fenrir-naru/gpib-usbcdc/firmware/f38x_usb.c

/*
 * Copyright (c) 2015, M.Naruoka (fenrir)
 * All rights reserved.
 *
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
 * THIS SOFTWARE IS PROVIDED BY THE COPYRIGHT HOLDERS AND CONTRIBUTORS "AS IS"
 * AND ANY EXPRESS OR IMPLIED WARRANTIES, INCLUDING, BUT NOT LIMITED TO,
 * THE IMPLIED WARRANTIES OF MERCHANTABILITY AND FITNESS FOR A PARTICULAR PURPOSE
 * ARE DISCLAIMED. IN NO EVENT SHALL THE COPYRIGHT HOLDER OR CONTRIBUTORS
 * BE LIABLE FOR ANY DIRECT, INDIRECT, INCIDENTAL, SPECIAL, EXEMPLARY,
 * OR CONSEQUENTIAL DAMAGES (INCLUDING, BUT NOT LIMITED TO,
 * PROCUREMENT OF SUBSTITUTE GOODS OR SERVICES;
 * LOSS OF USE, DATA, OR PROFITS; OR BUSINESS INTERRUPTION)
 * HOWEVER CAUSED AND ON ANY THEORY OF LIABILITY, WHETHER IN CONTRACT,
 * STRICT LIABILITY, OR TORT (INCLUDING NEGLIGENCE OR OTHERWISE)
 * ARISING IN ANY WAY OUT OF THE USE OF THIS SOFTWARE,
 * EVEN IF ADVISED OF THE POSSIBILITY OF SUCH DAMAGE.
 *
 */

#include <stdio.h>
#include <string.h>

#include "c8051f380.h"
#include "main.h"
#include "f38x_usb_register.h"
#include "f38x_usb.h"
#include "usb_descriptor.h"

#include "usb_std_req.h"
#include "usb_other_req.h"

#include "usb_cdc.h"

#include "util.h"

// Holds the current USB State
usb_state_t usb_state;

ep0_setup_t ep0_setup;
ep0_data_t ep0_data;
volatile __bit ep0_request_completed;

// Holds the status for each endpoint
BYTE __xdata usb_ep_stat[7];

static __xdata unsigned int ep_out_stored[3];
#define count_ep_out(index) ep_out_stored[index - 1]

static const __code unsigned int ep_size[] = {
  PACKET_SIZE_EP0,
  PACKET_SIZE_EP1,
  PACKET_SIZE_EP2,
  PACKET_SIZE_EP3
};

static __code void(* __xdata stall_callbacks[6])();

#define EP_INDEX_2_LINER_INDEX(dir, ep_index) \
((dir == DIR_IN) ? (ep_index - 1) : (ep_index + 2))

// consider into both interrupt and user invoked cases
#ifdef USE_ASM_FOR_SFR_MANIP
#define CRITICAL_USB0_SPECIAL(func) \
{ \
  BYTE eie1_backup = EIE1; \
  {__asm anl _EIE1,SHARP ~0x02 __endasm; } \
  { \
    func; \
  } \
  if(eie1_backup & 0x02){ \
    {__asm orl _EIE1,SHARP 0x02 __endasm; } \
  } \
}
#else
#define CRITICAL_USB0_SPECIAL(func) \
{ \
  BYTE eie1_backup = EIE1; \
  EIE1 &= ~(0x02); \
  { \
    func; \
  } \
  if(eie1_backup & 0x02){EIE1 |= 0x02;} \
}
#endif

/**
 * Read from the selected endpoint FIFO
 * 
 * @param ptr_data read data destination
 * @param index target EP index
 * @param u_num_bytes number of bytes to unload
 * @return number to read
 */
static unsigned int fifo_read_C(
    BYTE* ptr_data, 
    unsigned int u_num_bytes,
    unsigned char index){
  
  // Check if >0 bytes requested,
  if(u_num_bytes){
    
    unsigned int read_count = u_num_bytes;
  
    // Set address and auto-read to initiate first read
    USB0ADR = (FIFO_EP0 + index) | 0xC0;
  
    // Wait for BUSY->'0' (data ready)
    while(USB0ADR & 0x80);
  
    // Unload <NumBytes> from the selected FIFO
    if(ptr_data){
      
      while(--read_count){
        // Copy data byte
        *(ptr_data++) = USB0DAT;
        
        // Wait for BUSY->'0' (data ready)
        while(USB0ADR & 0x80);
      }
      
      // Clear auto-read
      USB0ADR &= ~0x40;
      
      // Copy data byte
      *(ptr_data++) = USB0DAT;
    }else{
      volatile BYTE c;
      while(--read_count){
        // Copy data byte
        c = USB0DAT;
        
        // Wait for BUSY->'0' (data ready)
        while(USB0ADR & 0x80);              
      }

      // Clear auto-read
      USB0ADR &= ~0x40;

      // Copy data byte
      c = USB0DAT;
    }
  }
  
  return u_num_bytes;
}
#define fifo0_read_C(ptr_data, u_num_bytes) \
fifo_read_C(ptr_data, u_num_bytes, 0)

typedef struct {
  BYTE *array;
  BYTE c;
} write_target_t;

/**
 * Write to the selected endpoint FIFO
 * 
 * @param target write data source
 * @param u_num_bytes number of bytes to unload
 * @param addr target address
 * @return number to write
 */
static unsigned int fifo_write_C(
    write_target_t *target,
    unsigned int u_num_bytes,
    unsigned char index){
  
  if(u_num_bytes > ep_size[index]){
    u_num_bytes = ep_size[index];
  }

  // If >0 bytes requested,
  if(u_num_bytes){
    unsigned int remain = u_num_bytes;

    BYTE *ptr = target->array;
      
    // Wait for BUSY->'0' (register available)
    while(USB0ADR & 0x80);
    
    // Set address (mask out bits7-6)
    USB0ADR = (FIFO_EP0 + index);
  
    if(ptr){
      // Write <NumBytes> to the selected FIFO
      while(remain--){
        USB0DAT = *(ptr++);
      }
      target->array = ptr; // advance pointer
    }else{
      // Write <NumBytes> to the selected FIFO
      BYTE c = target->c;
      while(remain--){
        USB0DAT = c;
      }
    }
  }
  
  return u_num_bytes;
}
#define fifo0_write_C(target, u_num_bytes) \
fifo_write_C(target, u_num_bytes, 0)

/**
 * Handle IN 1-3 Endpoint interrupts, which are generated when
 * 1. An IN packet is successfully transferred to the host.
 * 2. Software writes 1 to the FLUSH bit (EINCSRL.3) when the target FIFO is not empty.
 * 3. Hardware generates a STALL condition.
 * 
 * @param ep_index Index of Endpoint
 */
static void usb_handle_in(unsigned char ep_index){
  
  BYTE control_reg;

  // Set index to EP ep_index
  POLL_WRITE_BYTE(INDEX, ep_index);
  
  // Read contol register for EP ep_index
  POLL_READ_BYTE(EINCSR1, control_reg);

  // Clear sent stall and flush FIFO if last packet returned a stall
  if(control_reg & rbInSTSTL){
    __code void (*callback_func)()
        = stall_callbacks[EP_INDEX_2_LINER_INDEX(DIR_IN, ep_index)];
    POLL_WRITE_BYTE(EINCSR1, 
        (control_reg & (rbInCLRDT | ~rbInSTSTL)));
    if(callback_func){callback_func();}
  }
}

/**
 * Handle OUT Endpoint interrupts, which are generated when
 * 1. Hardware sets the OPRDY bit (EINCSRL.0) to 1.
 * 2. Hardware generates a STALL condition.
 * 
 * @param ep_index Index of Endpoint
 * 
 */
static void usb_handle_out(unsigned char ep_index){
  BYTE control_reg;

  // Set index
  POLL_WRITE_BYTE(INDEX, ep_index);
  POLL_READ_BYTE(EOUTCSR1, control_reg);
  
  // Clear sent stall bit if last packet was a stall
  if(control_reg & rbOutSTSTL){
    __code void (*callback_func)()
        = stall_callbacks[EP_INDEX_2_LINER_INDEX(DIR_OUT, ep_index)]; 
    POLL_WRITE_BYTE(EOUTCSR1, 
        (control_reg & (rbOutCLRDT | ~rbOutSTSTL)));
    if(callback_func){callback_func();}
  }

  // Otherwise read received packet from host
  else if(control_reg & rbOutOPRDY){
    BYTE b1, b2;
    POLL_READ_BYTE(EOUTCNTH, b1);
    POLL_READ_BYTE(EOUTCNTL, b2);
    count_ep_out(ep_index) = ((((unsigned int)b1) << 8) | b2);
  }
}

/**
 * Decode Incoming Setup requests
 * Load data packets on fifo while in transmit mode
 * 
 */
static void handle_setup(){
  // Temporary storage for EP control register
  BYTE control_reg;

  // Set Index to Endpoint Zero
  POLL_WRITE_BYTE(INDEX, EP0_IDX);
  
  // Read control register
  POLL_READ_BYTE(E0CSR, control_reg);

  // Handle Status Phase of Set Address command
  if(usb_ep0_status == EP_ADDRESS){
    POLL_WRITE_BYTE(FADDR, ep0_setup.wValue.c[LSB]);
    usb_ep0_status = EP_IDLE;
  }

  // If last packet was a sent stall, reset STSTL
  // bit and return EP0 to idle state
  if (control_reg & rbSTSTL){
    POLL_WRITE_BYTE(E0CSR, 0);
    usb_ep0_status = EP_IDLE;
    return;
  }

  // If last setup transaction was ended prematurely then set
  if(control_reg & rbSUEND){
    POLL_WRITE_BYTE(E0CSR, rbDATAEND);
    
    // Serviced Setup End bit and return EP0 to idle state
    POLL_WRITE_BYTE(E0CSR, rbSSUEND);
    usb_ep0_status = EP_IDLE;
  }

  // If Endpoint 0 is in idle mode
  if(usb_ep0_status == EP_IDLE){
    
    // Make sure that EP 0 has an Out Packet ready from host
    // although if EP0 is idle, this should always be the case
    if(control_reg & rbOPRDY){                                 
      
      fifo0_read_C((BYTE *)&ep0_setup, 8);
      
      ep0_request_completed = FALSE;
      
      // Call correct subroutine to handle each kind of standard request
      switch(ep0_setup.bmRequestType & DRT_MASK){
        // Standard device request
        case DRT_STD:     usb_standard_request(); break;
        case DRT_CLASS:   usb_class_request();    break;
        case DRT_VENDOR:  usb_vendor_request();   break;
      }
      
      // Set index back to endpoint 0
      POLL_WRITE_BYTE(INDEX, EP0_IDX);
      
      if(!ep0_request_completed){
        // Send stall to host if invalid request
        POLL_WRITE_BYTE(E0CSR, rbSDSTL);
        // Put the endpoint in stall status
        usb_ep0_status = EP_STALL;
        return;
      }
      
      // Indicate setup packet has been serviced
      control_reg = rbSOPRDY;
      if(usb_ep0_status == EP_IDLE){
        control_reg |= rbDATAEND;
      }
      POLL_WRITE_BYTE(E0CSR, control_reg);
    }
  } 

  // See if the endpoint has data to transmit to host
  switch(usb_ep0_status){
    case EP_TX: {
      // Make sure you don't overwrite last packet
      if (control_reg & rbINPRDY){break;}
        
      // Read control register
      POLL_READ_BYTE(E0CSR, control_reg);          
     
      // Check to see if Setup End or Out Packet received, if so                            
      // do not put any new data on FIFO
      if((control_reg & rbSUEND) && (control_reg & rbOPRDY)){break;}
              
      // Add In Packet ready flag to E0CSR bitmask
      control_reg = rbINPRDY;
     
      {
        unsigned int written;

        write_target_t target;
        target.array = ep0_data.buf;

        written = fifo0_write_C(&target, ep0_data.size);

        if(ep0_data.size > written){

          ep0_data.size -= written;
          ep0_data.buf = target.array; // Get advanced data pointer
        }else if(written < ep_size[0]){
          // check whether the last write size is less than maximum packet size, which requires additional ZLP
          
          if(ep0_data.callback){ep0_data.callback();}
          
          // Add Data End bit to bitmask
          control_reg |= rbDATAEND;
        
          // Return EP 0 to idle state
          usb_ep0_status = EP_IDLE;
        }
      }
      
      // Write mask to E0CSR
      POLL_WRITE_BYTE(E0CSR, control_reg);
      
      break;
    }
    case EP_RX: {
      // Verify packet was received
      if(control_reg & rbOPRDY){
        
        BYTE recieved;
        
        control_reg = rbSOPRDY;
  
        // get data bytes on the FIFO
        POLL_READ_BYTE(E0CNT, recieved);
        
        // Empty the FIFO
        // FIFO must be read out just the size it has,
        // otherwise the FIFO pointer on the SIE goes out of synch.
        fifo0_read_C((BYTE*)ep0_data.buf, recieved);
        
        if(ep0_data.size > recieved){
          // Update the scheduled number to be received
          ep0_data.size -= recieved;
          
          // Advance the pointer
          ep0_data.buf += recieved;
        }else{
          // Meet the end of the data stage
          ep0_data.size = 0;
          
          // Signal end of data stage
          control_reg |= rbDATAEND;
          
          usb_ep0_status = EP_IDLE;
  
          ep0_data.callback();
        }
  
        POLL_WRITE_BYTE(E0CSR, control_reg);
      }
      break;
    }
  }
}

/**
 * Resume normal USB operation
 * 
 * Add code to turn on anything turned off when entering suspend mode
 */
static void resume(){ 
  
}

/**
 * Enter suspend mode after suspend signalling is present on the bus
 * 
 * Add power-down features here if you wish to
 * reduce power consumption during suspend mode
 */
static void suspend(){
  
}

volatile __xdata BYTE usb_frame_num;

/**
 * Set state to default
 * Clear USB Inhibit bit
 */
static void reset(){
  // Set device state to default
  usb_state = DEV_DEFAULT;
  
  // Set default Endpoint Status
  usb_ep0_status = EP_IDLE;
  
  // clear EP1-3 states, stall callback funcs, and out counters
  {
    unsigned char ep_index;
    for(ep_index = 1; ep_index <= 3; ep_index++){
      usb_ep_stat[ep_index] = EP_HALT;
      stall_callbacks[EP_INDEX_2_LINER_INDEX(DIR_IN, ep_index)] = NULL;
      stall_callbacks[EP_INDEX_2_LINER_INDEX(DIR_OUT, ep_index)] = NULL;
      count_ep_out(ep_index) = 0;
    }
  }
  
  usb_frame_num = 0;

  // Clear USB inhibit bit to enable USB suspend detection
  POLL_WRITE_BYTE(POWER, 0x01);
  
  // initialize class
  usb_class_init();
}

static void enable_phy(){
#ifdef _USB_LOW_SPEED_
  USB0XCN = 0xC0;                // Enable transceiver; select low speed
  POLL_WRITE_BYTE(CLKREC, 0xA0); // Enable clock recovery; single-step mode disabled; low speed mode enabled
#else
  USB0XCN = 0xE0;                // Enable transceiver; select full speed
  POLL_WRITE_BYTE(CLKREC, 0x80); // Enable clock recovery, single-step mode disabled
#endif /* _USB_LOW_SPEED_ */
  reset();
  EIE1 |= 0x02; // Enable USB0 Interrupts
}

/**
 * USB Initialization
 *
 * Initialize USB0
 * Enable USB0 interrupts
 * Enable USB0 transceiver
 * Enable USB0 with suspend detection
 */
void usb0_init(){
  POLL_WRITE_BYTE(POWER,  0x08); // Force Asynchronous USB Reset
  POLL_WRITE_BYTE(IN1IE,  0x0F); // Enable Endpoint 0-3 in interrupts
  POLL_WRITE_BYTE(OUT1IE, 0x0F); // Enable Endpoint 0-3 out interrupts
  POLL_WRITE_BYTE(CMIE,   0x07); // Enable Reset, Resume, and Suspend interrupts

  if(REG01CN & 0x40){
    usb_mode = USB_CABLE_CONNECTED;
    enable_phy();
    wait_ms(100);
  }else{
    usb_mode = USB_INACTIVE;
  }
}

/**
 * Top-level USB ISR
 * 
 * Called after any USB type interrupt, this handler determines which type
 * of interrupt occurred, and calls the specific routine to handle it.
 * 
 */
void usb_isr() __interrupt (INTERRUPT_USB0) {
  BYTE bCommon, bIn, bOut;
  POLL_READ_BYTE(CMINT, bCommon);      // Read all interrupt registers
  POLL_READ_BYTE(IN1INT, bIn);         // this read also clears the register
  POLL_READ_BYTE(OUT1INT, bOut);

  // Handle Resume interrupt
  if(bCommon & rbRSUINT){resume();}
    
  // Handle Setup packet received
  // or packet transmitted if Endpoint 0 is transmit mode 
  if(bIn & rbEP0){handle_setup();}
  
  {
    unsigned char ep_index, ep_mask = 0x02;
    for(ep_index = 1; ep_index <= 3; ep_index++, ep_mask <<= 1){
      
      // Handle In packet received
      if(bIn & ep_mask){usb_handle_in(ep_index);}
      
      // Handle Out packet received, take data off OUT endpoint
      if(bOut & ep_mask){usb_handle_out(ep_index);}
    }
  }
  
  // Handle Start of Frame interrupt
  //if(bCommon & rbSOF){}
  
  // Handle Suspend interrupt
  if(bCommon & rbSUSINT){suspend();}
  
  // Handle Reset interrupt
  if(bCommon & rbRSTINT){reset();}
}

volatile usb_mode_t usb_mode;

static unsigned int usb_tx(
    write_target_t *target,
    unsigned int count,
    unsigned char index){
  unsigned int count_orig = count, add;
  do{
    add = 0;
    CRITICAL_USB0_SPECIAL(
      BYTE control_reg;

      // Check endpoint is not halted
      if(ep_strip_owner(usb_ep_status(DIR_IN, index)) != EP_HALT){

        // Set index to EP ep_index
        POLL_WRITE_BYTE(INDEX, index);

        // Read control register for EP ep_index
        POLL_READ_BYTE(EINCSR1, control_reg);
        
        // Register data for transmission
        if(!(control_reg & (rbInSDSTL | rbInFLUSH | rbInINPRDY))){

          // Clear underrun bit if it was set
          //if(control_reg & rbInUNDRUN){} // TODO

          // Put new data on FIFO
          add = fifo_write_C(target, count, index);

          // Set In Packet ready bit, indicating fresh data on FIFO
          POLL_WRITE_BYTE(EINCSR1, rbInINPRDY);
        }
      }
    );
    
    if(!add){break;}
    count -= add;
  }while(count);
  return count_orig - count;
}

unsigned int usb_write(
    BYTE* ptr_buf,
    unsigned int count,
    unsigned char index){
  write_target_t target;
  target.array = ptr_buf;  
  return usb_tx(&target, count, index);
}

unsigned int usb_fill(
    BYTE c,
    unsigned int count,
    unsigned char index){
  write_target_t target = {NULL, c};
  return usb_tx(&target, count, index);
}

unsigned int usb_count_ep_out(unsigned char index){
  unsigned int res;
  CRITICAL_USB0_SPECIAL(
    res = count_ep_out(index);
  );
  return res;
}

unsigned int usb_read(
    BYTE* ptr_buf,
    unsigned int count,
    unsigned char index){
  CRITICAL_USB0_SPECIAL(
    if(count_ep_out(index) < count){
      count = count_ep_out(index);
    }
    count = fifo_read_C(ptr_buf, count, index);
    count_ep_out(index) -= count;
    if((count > 0) && (count_ep_out(index) == 0)){
      POLL_WRITE_BYTE(INDEX, index);
      POLL_WRITE_BYTE(EOUTCSR1, 0);
    }
  );
  return count;
}

unsigned int usb_skip(
    unsigned int count,
    unsigned char index){
  return usb_read(NULL, count, index);
}

void usb_flush(unsigned char index){
  // Clear Out Packet ready bit
  usb_read(NULL, ep_size[index], index);
}

void usb_status_lock(unsigned char dir, unsigned char ep_index){
  CRITICAL_USB0_SPECIAL(
    usb_ep_status(dir, ep_index) |= EP_OWNED_BY_USER;
  );
}

void usb_status_unlock(unsigned char dir, unsigned char ep_index){
  CRITICAL_USB0_SPECIAL(
    usb_ep_status(dir, ep_index) &= ~EP_OWNED_BY_USER;
  );
}

void usb_stall(unsigned char dir, unsigned char ep_index,  
    __code void(*callback)()){
  CRITICAL_USB0_SPECIAL(
    usb_ep_status(dir, ep_index) 
        = (usb_ep_status(dir, ep_index) & EP_OWNED_BY_USER) | EP_HALT;
  
    // Set index to EP ep_index
    POLL_WRITE_BYTE(INDEX, ep_index);
    
    // send a stall immediately
    if(dir == DIR_IN){
      POLL_WRITE_BYTE(EINCSR1, rbInSDSTL);
      stall_callbacks[EP_INDEX_2_LINER_INDEX(DIR_IN, ep_index)] = callback;
    }else{
      POLL_WRITE_BYTE(EOUTCSR1, rbOutSDSTL);
      stall_callbacks[EP_INDEX_2_LINER_INDEX(DIR_OUT, ep_index)] = callback;
    }
  );
}

void usb_clear_halt(unsigned char dir, unsigned char ep_index){
  CRITICAL_USB0_SPECIAL(
    usb_ep_status(dir, ep_index) 
        = (usb_ep_status(dir, ep_index) & EP_OWNED_BY_USER) | EP_IDLE;
    
    // Set index to EP ep_index
    POLL_WRITE_BYTE(INDEX, ep_index);
    
    // clear flag
    if(dir == DIR_IN){
      POLL_WRITE_BYTE(EINCSR1, 0);
    }else{
      POLL_WRITE_BYTE(EOUTCSR1, 0);
    }
  );
}

void usb_polling(){
  
  switch(usb_mode){
    case USB_INACTIVE:
      if(REG01CN & 0x40){
        usb_mode = USB_CABLE_CONNECTED;
        enable_phy();
      }
      return;
    case USB_CABLE_CONNECTED:
      break;
    case USB_CDC_READY:
      usb_mode = USB_CDC_ACTIVE;
      break;
    case USB_CDC_ACTIVE:
      cdc_polling();
      break;
  }
  
  CRITICAL_USB0_SPECIAL(
    POLL_READ_BYTE(FRAMEL, usb_frame_num);
  );

  if(!(REG01CN & 0x40)){
    EIE1 &= ~0x02;  // Disable USB0 Interrupts
    USB0XCN = 0;
    usb_mode = USB_INACTIVE;
  }
}
